Whackalenso/pocket-traveller/media/backpack2.jpeg

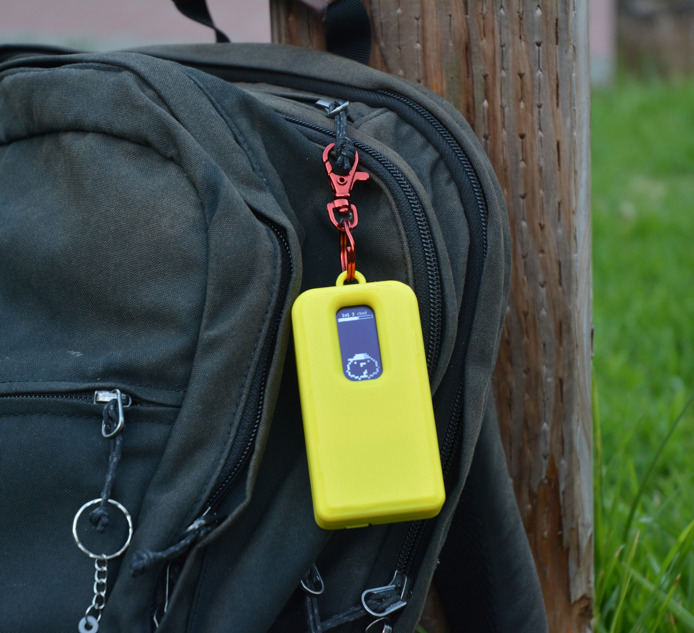
media/backpack2.jpeg
