Whackalenso/pocket-traveller/media/photoshoot1.jpeg

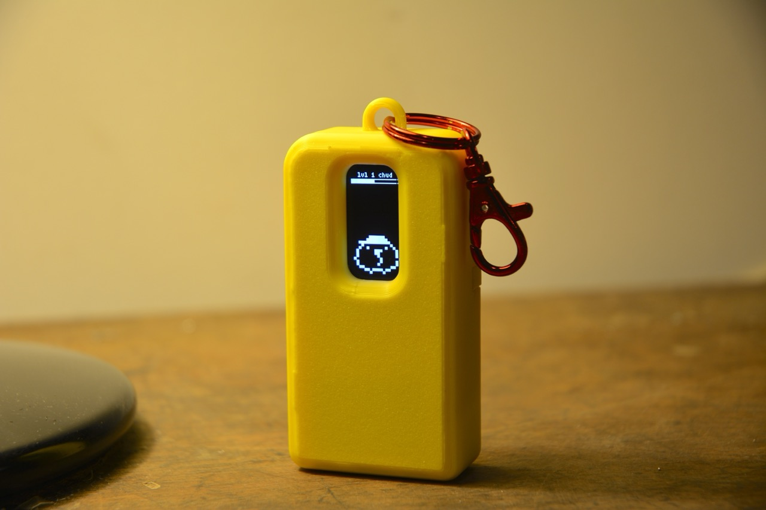
media/photoshoot1.jpeg
