Whackalenso/pocket-traveller/lab/calibration/cal_5.csv

t | variance | rhythm
10.0 | 171006280.0 | 0.438
10.5 | 163217540.0 | 0.473
11.0 | 161680270.0 | 0.451
11.5 | 175764780.0 | 0.535
12.0 | 192704140.0 | 0.491
12.5 | 170148060.0 | 0.484
13.0 | 181017080.0 | 0.457
13.5 | 182154360.0 | 0.465
14.0 | 173829980.0 | 0.498
14.5 | 156102620.0 | 0.450
15.0 | 169664780.0 | 0.451
15.5 | 170037420.0 | 0.454
16.0 | 150654000.0 | 0.461
16.5 | 164855020.0 | 0.460
17.0 | 182079080.0 | 0.496
17.5 | 164022540.0 | 0.477
18.0 | 169850320.0 | 0.473
18.5 | 164536700.0 | 0.515
19.0 | 154984910.0 | 0.460
19.5 | 130120840.0 | 0.544
20.0 | 138170340.0 | 0.527
20.5 | 143711900.0 | 0.505
21.0 | 140305200.0 | 0.380
21.5 | 142042280.0 | 0.458
22.0 | 155714720.0 | 0.558
22.5 | 159903250.0 | 0.482
23.0 | 150727680.0 | 0.330
23.5 | 154915520.0 | 0.420
24.0 | 165025400.0 | 0.363
24.5 | 154962080.0 | 0.455
25.0 | 140605720.0 | 0.594
25.5 | 152558540.0 | 0.463
26.0 | 148184910.0 | 0.389
26.5 | 145275340.0 | 0.393
27.0 | 151393230.0 | 0.383
27.5 | 165485080.0 | 0.328
28.0 | 157597480.0 | 0.342
28.5 | 153577700.0 | 0.355
29.0 | 166313340.0 | 0.423
29.5 | 151945580.0 | 0.373
30.0 | 142201800.0 | 0.394
30.5 | 156391160.0 | 0.286
31.0 | 157824300.0 | 0.294
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
