Whackalenso/pocket-traveller/lab/calibration/cal_6.csv

t | variance | rhythm
10.0 | 7206.5 | 0.229
10.5 | 6751.9 | 0.324
11.0 | 6916.4 | 0.202
11.5 | 5472.3 | 0.140
12.0 | 4554.7 | 0.294
12.5 | 7064.0 | 0.134
13.0 | 12745.5 | 0.141
13.5 | 18801.8 | 0.233
14.0 | 30308.0 | 0.213
14.5 | 89896.6 | 0.267
15.0 | 299621.9 | 0.261
15.5 | 891218.3 | 0.308
16.0 | 1130372.6 | 0.313
16.5 | 2897856.2 | 0.060
17.0 | 2922832.2 | 0.050
17.5 | 2804060.0 | 0.072
18.0 | 2358032.2 | 0.077
18.5 | 2469201.0 | 0.123
19.0 | 747705.8 | 0.120
19.5 | 1305222.4 | 0.179
20.0 | 1376101.9 | 0.231
20.5 | 1393854.5 | 0.240
21.0 | 1478668.5 | 0.218
21.5 | 1419121.4 | 0.233
22.0 | 871581.0 | 0.205
22.5 | 649918.7 | 0.252
23.0 | 640104.2 | 0.157
23.5 | 362913.4 | 0.192
24.0 | 259041.6 | 0.147
24.5 | 244064.4 | 0.211
25.0 | 432885.7 | 0.245
25.5 | 911932.2 | 0.203
26.0 | 948636.0 | 0.175
26.5 | 1005948.8 | 0.138
27.0 | 1050772.0 | 0.113
27.5 | 944839.8 | 0.173
28.0 | 530794.6 | 0.296
28.5 | 1135006.5 | 0.280
29.0 | 1348460.6 | 0.339
29.5 | 1519926.6 | 0.367
30.0 | 1572516.4 | 0.338
30.5 | 1583900.6 | 0.227
31.0 | 1004377.8 | 0.145
31.5 | 923224.9 | 0.229
32.0 | 783269.3 | 0.261
32.5 | 2138801.8 | 0.137
33.0 | 2368466.4 | 0.192
33.5 | 2262836.4 | 0.218
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
